richteel/gps_tracker/Case/gps.jpg

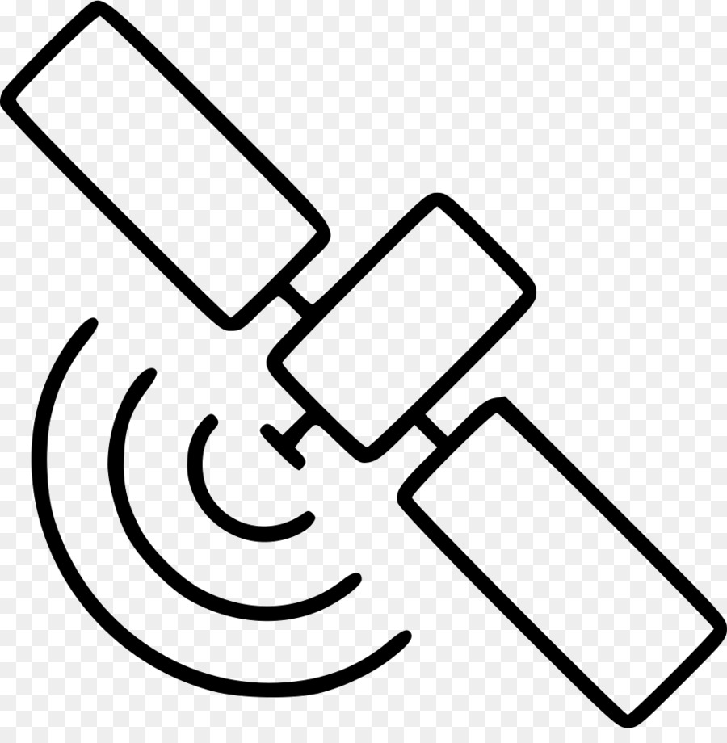
Case/gps.jpg
