richteel/gps_tracker/Case/gps_sat2.png

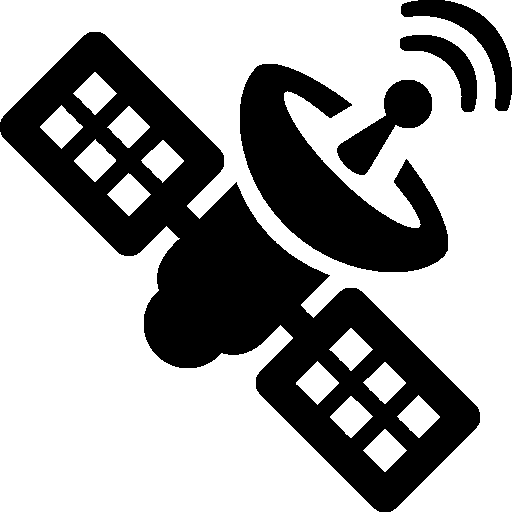
Case/gps_sat2.png
