richteel/gps_tracker/Case/gps_sat.png

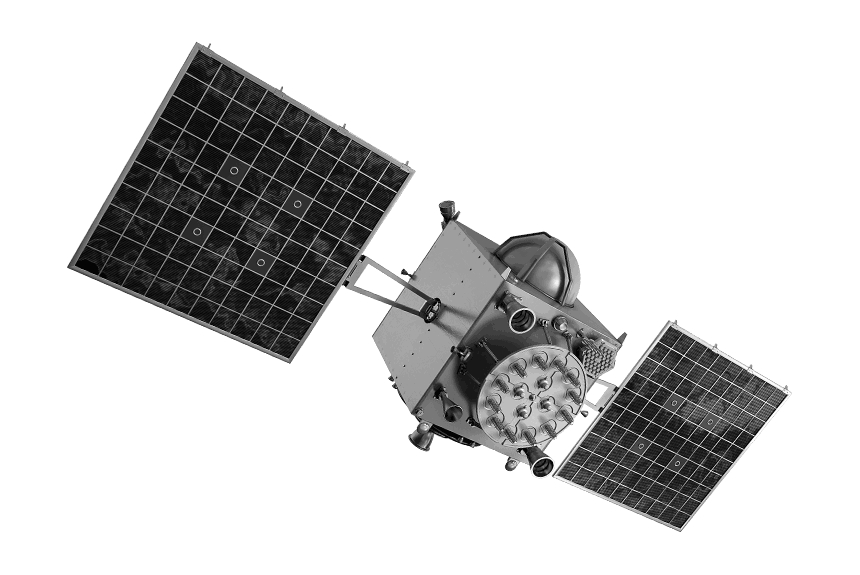
Case/gps_sat.png
