richteel/gps_tracker/docs/img/2cf106b1-79df-4a27-8504-c470ad124604.__CR0,0,970,300_PT0_SX970_V1___.jpg

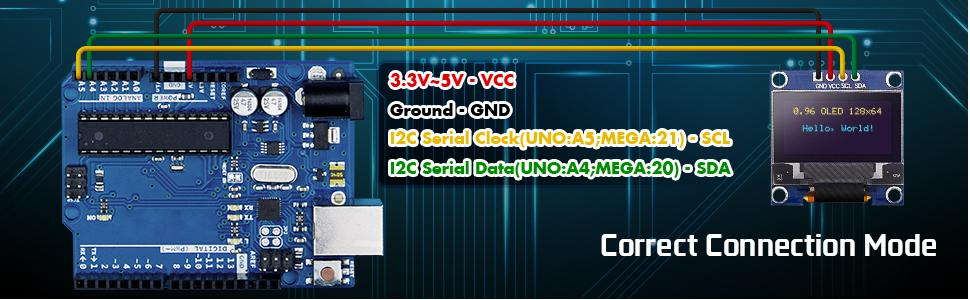
docs/img/2cf106b1-79df-4a27-8504-c470ad124604.__CR0,0,970,300_PT0_SX970_V1___.jpg
