richteel/gps_tracker/docs/img/02dcfc04-3a34-4587-9082-6839edc16a10.__CR0,0,970,600_PT0_SX970_V1___.jpg

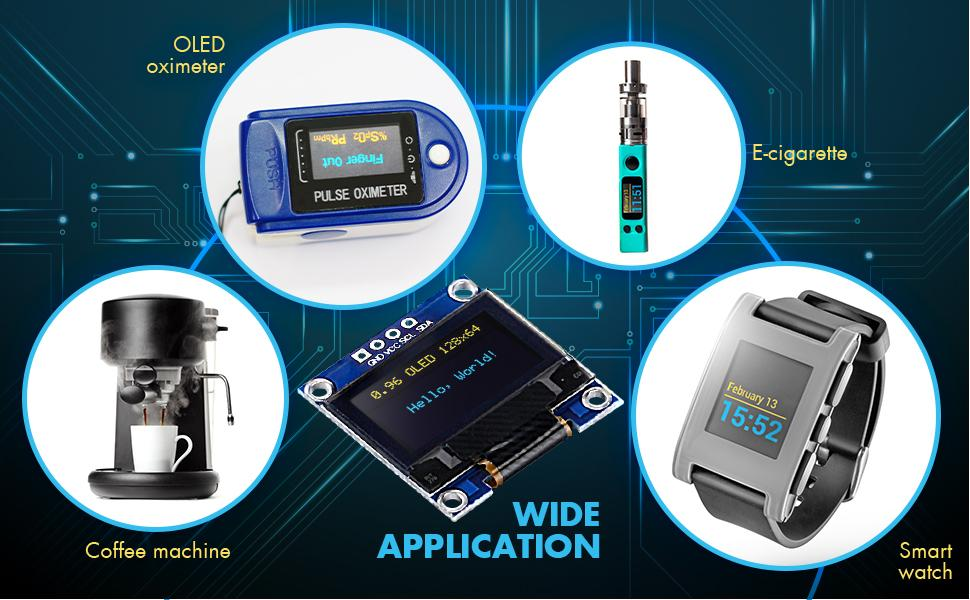
docs/img/02dcfc04-3a34-4587-9082-6839edc16a10.__CR0,0,970,600_PT0_SX970_V1___.jpg
