richteel/gps_tracker/docs/img/17daa6f5-d152-403f-8c28-235bc5477643.__CR0,0,970,600_PT0_SX970_V1___.jpg

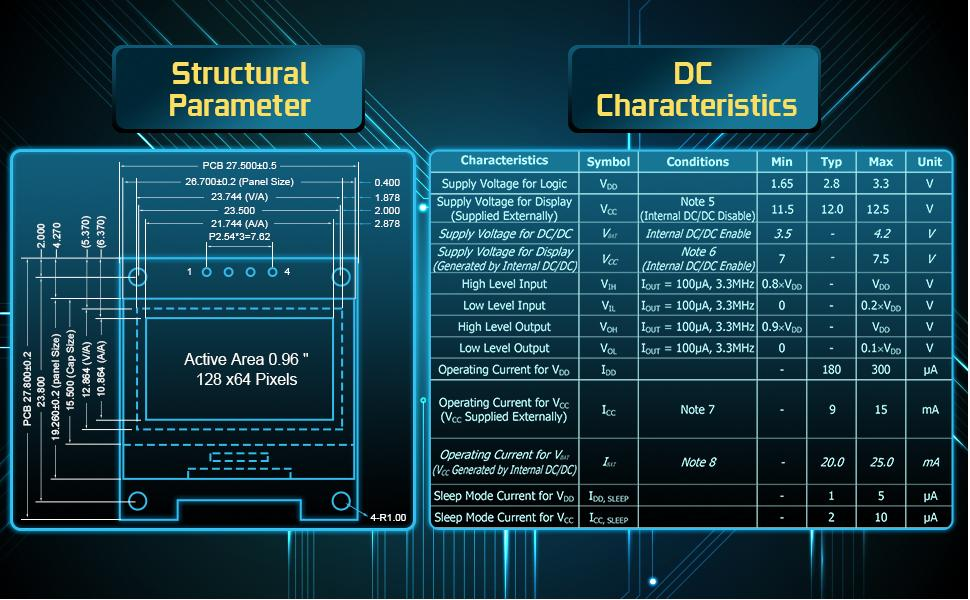
docs/img/17daa6f5-d152-403f-8c28-235bc5477643.__CR0,0,970,600_PT0_SX970_V1___.jpg
