richteel/gps_tracker/docs/img/gps_tracker.png

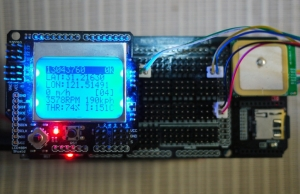
docs/img/gps_tracker.png
