richteel/gps_tracker/docs/PCB_Bottom.png

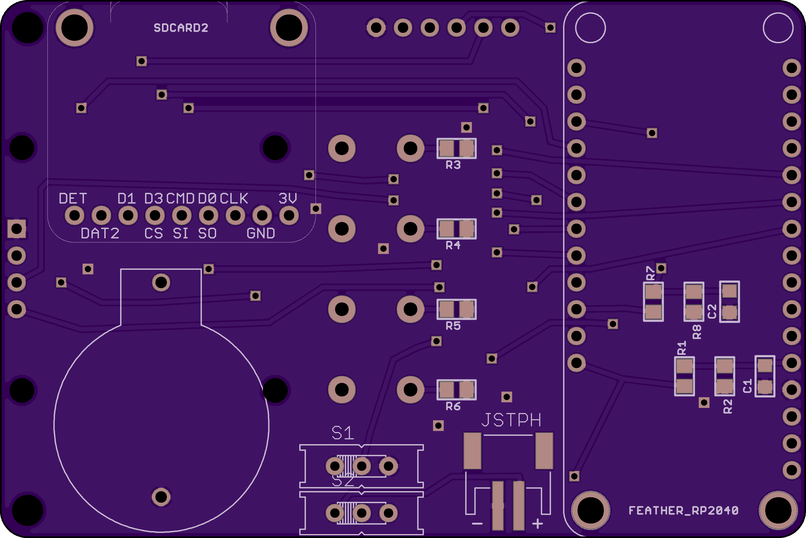
docs/PCB_Bottom.png
