richteel/gps_tracker/docs/PCB_Eagle.png

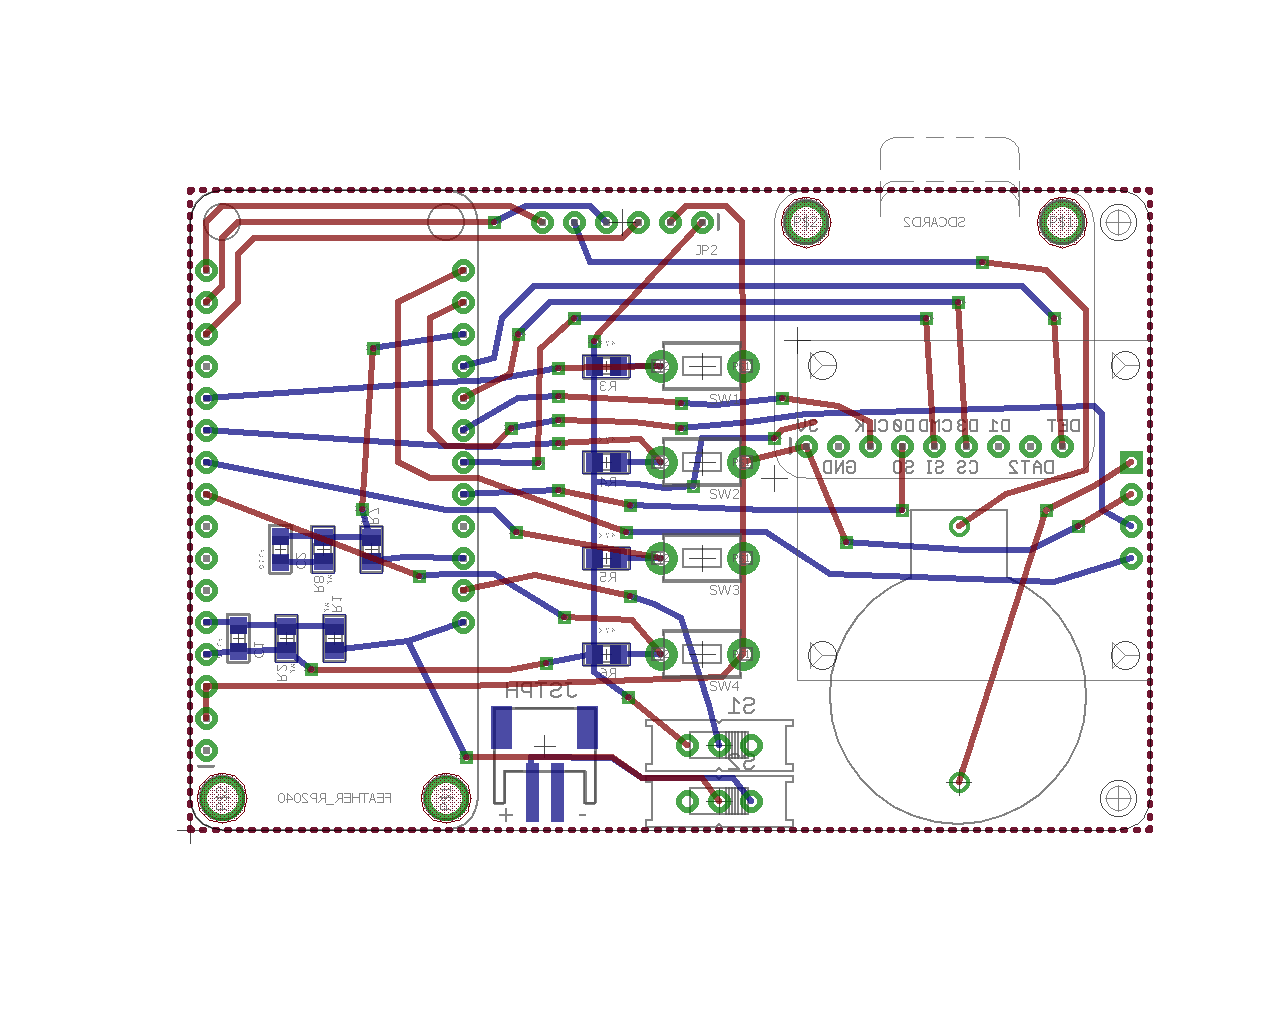
docs/PCB_Eagle.png
