richteel/gps_tracker/CircuitPython/dispItems.py

battery = {
    "voltage" : {"label" : " Batt:", "value": ""},
    "percent" : {"label" : " Batt:", "value": ""},
    "status" : {"label" : "Statu:", "value": ""}
}

gps = {
    "datetime" : {"label" : "", "value": ""},
    "lat" : {"label" : "  Lat:", "value": ""},
    "long" : {"label" : " Long:", "value": ""},
    "alt" : {"label" : "  Alt:", "value": ""},
    "heading" : {"label" : " Head:", "value": ""},
    "speed" : {"label" : "Speed:", "value": ""},
    "satellites" : {"label" : "  Sat:", "value": ""},
    "fixQ" : {"label" : "Fix Q:", "value": ""}
}

rtc = {
    "datetime" : {"label" : "", "value": ""},
    "unixtime" : {"label" : "", "value": ""}
}

sdcard = {
    "cardPresent" : {"label" : " Card:", "value": ""},
    "cardSizeMb" : {"label" : " Size:", "value": ""},
    "cardFreeMb" : {"label" : " Free:", "value": ""},
    "cardFiles" : {"label" : "Files:", "value": ""}
}

info = {
    "version" : {"label" : "  TeelSys GPS v0.3   ", "value": ""},
    "minMemory" : {"label" : "M Min:", "value": ""},
    "minMemoryDT" : {"label" : "DT", "value": ""},
    "gpsEnabled" : {"label" : "GPS E:", "value": ""},
    "sdcardEnabled" : {"label" : " SD E:", "value": ""}
}
