richteel/gps_tracker/CircuitPython/logItems.py

battery = {
    "voltage" : {"label" : "Batt V", "value": ""},
    "percent" : {"label" : "Batt %", "value": ""},
    "status" : {"label" : " Batt Status", "value": ""}
}

gps = {
    "datetime" : {"label" : "Date/Time", "value": ""},
    "lat" : {"label" : "Lat", "value": ""},
    "long" : {"label" : "Long", "value": ""},
    "alt" : {"label" : "Alt", "value": ""},
    "heading" : {"label" : "Heading", "value": ""},
    "speed" : {"label" : "Speed", "value": ""},
    "satellites" : {"label" : "Satellites", "value": ""},
    "fixQ" : {"label" : "Fix Quality", "value": ""},
    "fixQ3d" : {"label" : "Fix Quality 3D", "value": ""}
}

rtc = {
    "datetime" : {"label" : "Date/Time", "value": ""},
    "unixtime" : {"label" : "Epoch", "value": ""}
}

sdcard = {
    "cardPresent" : {"label" : "Card Present", "value": ""},
    "cardSizeMb" : {"label" : "Card Size (MB)", "value": ""},
    "cardFreeMb" : {"label" : "Free Space (MB)", "value": ""},
    "cardFiles" : {"label" : "File Count", "value": ""}
}

info = {
    "version" : {"label" : "  TeelSys GPS v0.2   ", "value": ""}
}
